howborn/smart-car-freescale/1.3D/整车预览.jpg

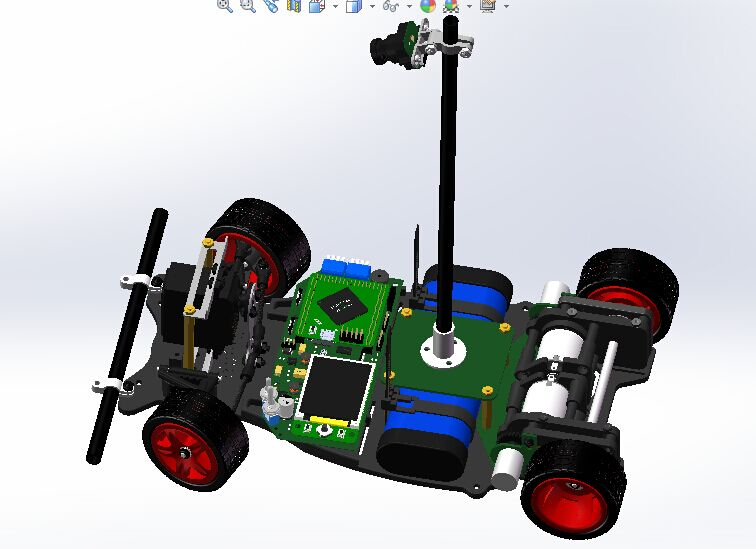
1.3D/整车预览.jpg
