howborn/smart-car-freescale/5.Photos/整车-黑白.jpg

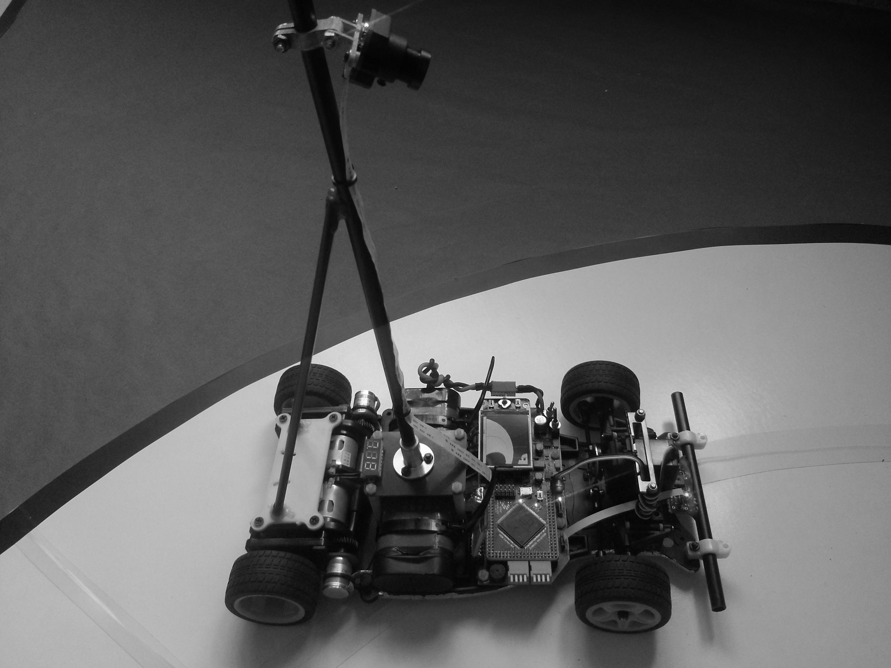
5.Photos/整车-黑白.jpg
