howborn/smart-car-freescale/1.3D/摄像头-三维图/摄像头-1.SLDASM

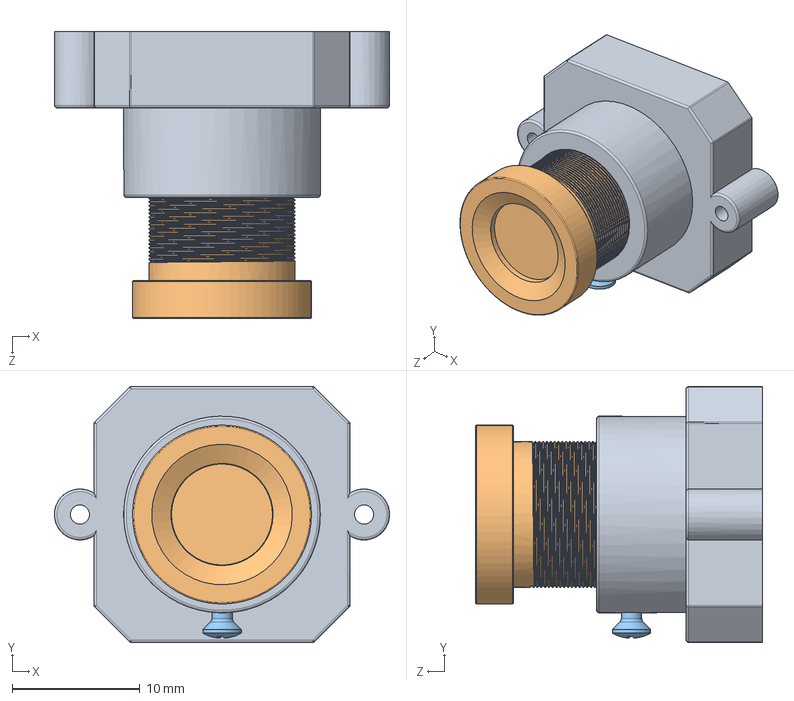
[picture p21: CAD file, 2018-04-18]
1.3D/摄像头-三维图/摄像头-1.SLDASM
26.2 x 20.1 x 22.5 mm
底座
镜头
螺钉
