howborn/smart-car-freescale/1.3D/摄像头-三维图/摄像头.SLDASM

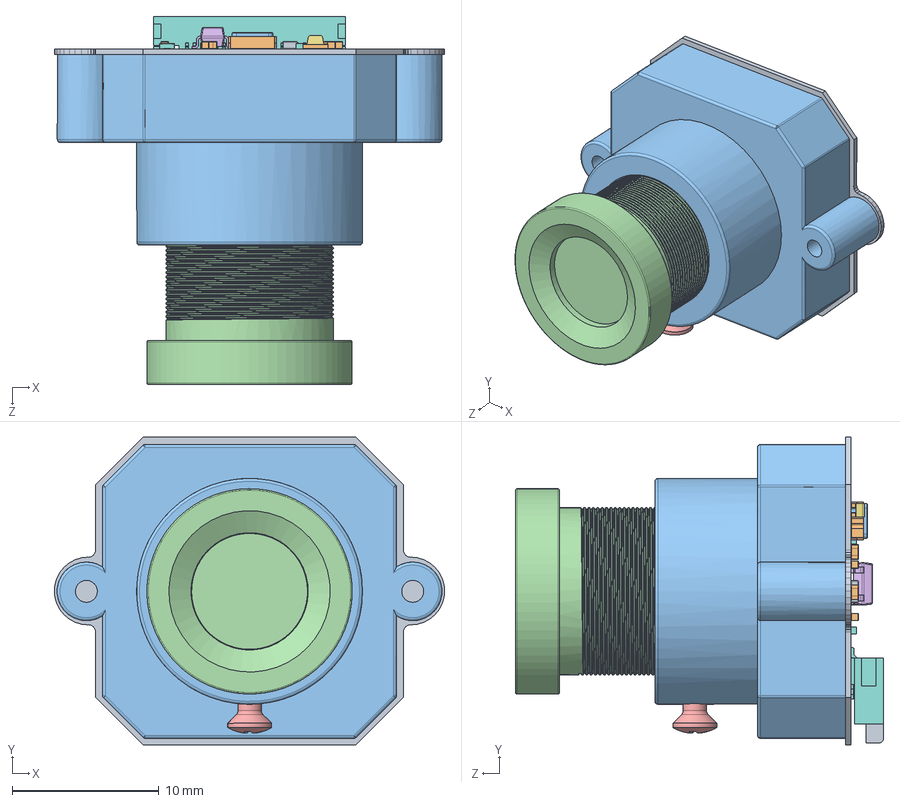
[picture p22: CAD file, 2018-04-18]
1.3D/摄像头-三维图/摄像头.SLDASM
26.6 x 21.0 x 25.1 mm
Board摄像头
User_Library-ASTX-H11_Pad
User_Library-ASTX-H11_Pad001
User_Library-ASTX-H11_Pad002
User_Library-ASTX-H11_ComponentPads
SOT23-5
CLCC-48-11.43x11.43mm
RES-0402 x 4
Chip_Inductor-0402_100505 x 2
User_Library-LTST-C190TBKT_Pad
User_Library-LTST-C190TBKT_Pad005
User_Library-LTST-C190TBKT_Pad001
User_Library-LTST-C190TBKT_Pad004
User_Library-LTST-C190TBKT_Pad003
User_Library-LTST-C190TBKT_Lens
FPC-ZIF-SMD-Horizontal-0.5-18
FPC-ZIF-SMD-Horizontal-0.5-18_2
CAP-0402 x 11
底座
镜头
螺钉
