howborn/smart-car-freescale/1.3D/编码器装配体_右.SLDASM

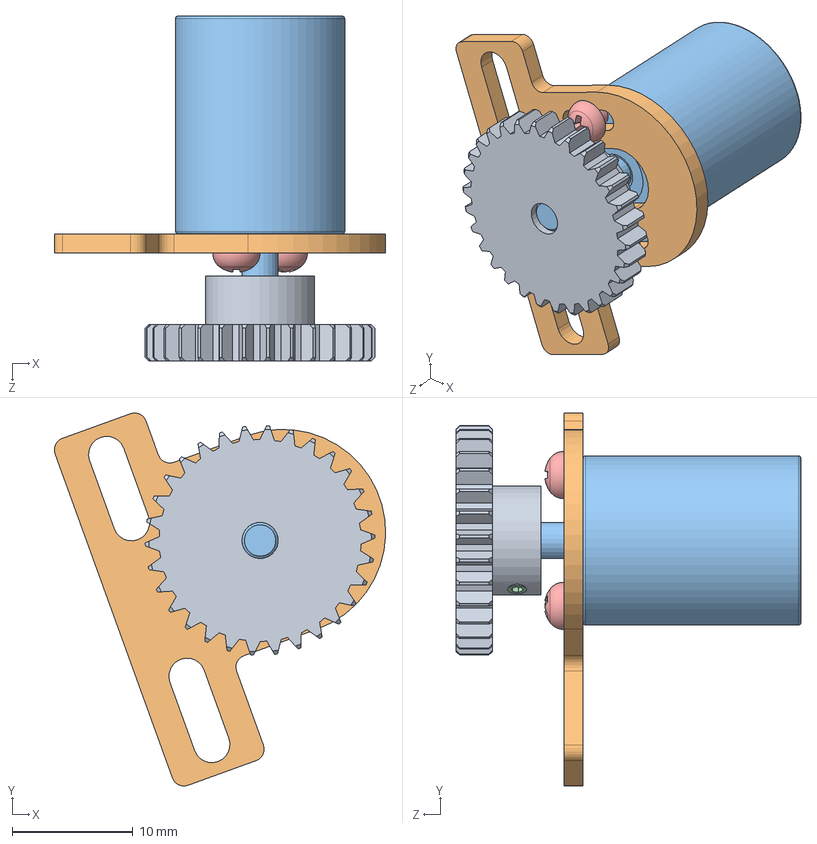
[picture p23: CAD file, 2018-04-18]
1.3D/编码器装配体_右.SLDASM
27.4 x 30.8 x 28.5 mm
编码器齿轮
编码器支架
测速编码器
紧钉螺钉-M2
十字半圆头螺钉-M2 x 2
