howborn/smart-car-freescale/1.3D/主板-三维图/主板_V1.0.SLDASM

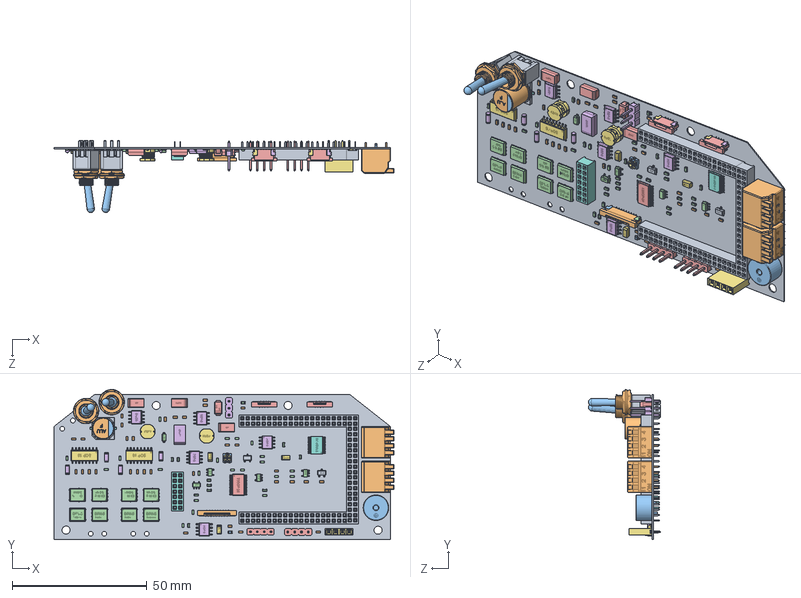
[picture p24: CAD file, 2018-04-18]
1.3D/主板-三维图/主板_V1.0.SLDASM
126.3 x 55.8 x 26.8 mm
Board主板_V1.0
Switch-Piano-DIP-4 x 2
Buzzer_9.5x6
CAP-0603 x 31
CaseC_6032-28 x 3
CaseD_7343-31
CaseA_3216-18 x 3
User_Library-ALU-F_Pins_1
User_Library-ALU-F_Fuss_1
User_Library-ALU-F_K_X_F6rper_1
User_Library-ALU-F_Beschriftung_1
Diode-SOD123
Diode-SMA
Diode-SMD-1206 x 4
Inductor-CD-54 x 2
User_Library-LTST-C190GKT_Pad005
User_Library-LTST-C190GKT_Pad001
User_Library-LTST-C190GKT_Pad004
User_Library-LTST-C190GKT_Pad003
User_Library-LTST-C190GKT_Lens
User_Library-LTST-C190GKT_Pad
User_Library-LTST-C190TBKT_Pad
User_Library-LTST-C190TBKT_Pad005
User_Library-LTST-C190TBKT_Pad001
User_Library-LTST-C190TBKT_Pad004
User_Library-LTST-C190TBKT_Pad003
User_Library-LTST-C190TBKT_Lens
DFN-5-5x6mm x 8
Pin-Header-2.54-Single-4 x 2
Pin-Header-2.54-Single-3
Female-Header-2.54-Single-4
Female-Header-2.00-Double-14
SOT323-3 x 2
RES-0603 x 32
User_Library-PVZ3A_PVZ3A_base_По_умолчанию
User_Library-PVZ3A_Pin1_По_умолчанию
User_Library-PVZ3A_Pin2_По_умолчанию
User_Library-PVZ3A_Pin2_По_умолчанию_2
User_Library-PVZ3A_PVZ3A_res_По_умолчанию
User_Library-PVZ3A_PVZ3A_con_По_умолчанию
SW-SMTS-102-1 x 2
SW-SMTS-102-2 x 2
SW-SMTS-102-3 x 2
SOT23-5 x 4
TSSOP-24
SOP-8 x 5
SOP-16 x 2
TSSOP-20
Female-Header-2.00-Double-40 x 3
ffc_fpc_affc20-18-050-shb-t_01
ffc_fpc_affc20-18-050-shb-t_02
ffc_fpc_affc20-18-050-shb-t_03
ffc_fpc_affc20-08-050-shb-t_01 x 2
ffc_fpc_affc20-08-050-shb-t_02 x 2
ffc_fpc_affc20-08-050-shb-t_03 x 2
