howborn/smart-car-freescale/3.Software/src/control.h

/**
 * --------------Smart_Car工程-----------------
 * @file Control.h
 * @version 0.0
 * @date 2015-2-7
 *
 *
 * 版权所有:  北华航天工学院 第十届飞思卡尔  摄像头2队
 * 硬件平台:  MK60FX512
 * 
 */
#ifndef __CONTROL_H__
#define __CONTROL_H__

void Direction_Control();
void Speed_Control();

#endif
