howborn/smart-car-freescale/3.Software/src/analyze.h

/**
 * --------------Smart_Car工程-----------------
 * @file Analyze.h
 * @version 0.0
 * @date 2015-2-7
 *
 *
 * 版权所有:  北华航天工学院 第十届飞思卡尔  摄像头2队
 * 硬件平台:  MK60FX512
 * 
 */
#ifndef __ANALYZE_H__
#define __ANALYZE_H__

void Find_Line(uint8 image[][H]);
void Get_Center_Line();
void Recognition_Type();

#endif
