howborn/smart-car-freescale/3.Software/src/delay.h

/**
 * --------------Smart_Car工程-----------------
 * @file Delay.h
 * @version 0.0
 * @date 2015-2-7
 *
 *
 * 版权所有:  北华航天工学院 第十届飞思卡尔  摄像头2队
 * 硬件平台:  MK60FX512
 * 
 */
#ifndef __DELAY_H__
#define __DELAY_H__

void Delayms(uint16 ms);
void Delayus(uint16 us);

#endif
