howborn/smart-car-freescale/3.Software/src/k60_card.h

#ifndef __K60_CARD_H__
#define __K60_CARD_H__

/*
 * 系统主频定义(CORE_CLK_MHZ)
 * 可选范围:
 * <MK60F15>
 * PLL_100       //100MHz 
 * PLL_120       //120MHz 是MK60F12的额定最高主频，再往上飞思卡尔可不质保
 * PLL_150       //150MHz 是MK60F15的额定最高主频，再往上飞思卡尔可不质保
 * PLL_180       //180MHz
 * PLL_200       //200MHz 如果超到200，发热很正常，烧了别找我>_>
 */
#if defined(USE_K60F15)
  #define CORE_CLK_MHZ        PLL_180
#endif


/*
 * 总线频率定义(BUS_CLK_MHZ)
 * 可选范围:
 *   不超过系统主频，但建议不超过100，超过100后会出现跑飞、发热现象
 *
*/
#if (defined(USE_K60F15))
  #define BUS_CLK_MHZ         60u
#endif   
/*
 * Flex总线频率定义(FLEXBUS_CLK_MHZ)
 * 可选范围:
 *   不超过50
 *
*/
#define FLEXBUS_CLK_MHZ     50u 
   
/*
 * Flash频率定义(FLASH_CLK_MHZ)
 * 可选范围:
 *   不超过25
 *
*/
#define FLASH_CLK_MHZ       25u    


/* 
 * 选择调试信息输出所有的串口号和波特率
 */
#define TERM_PORT           UART0
#define TERMINAL_BAUD       115200
#define UART_R_PORT         PTB16
#define UART_T_PORT         PTB17

/*
 * 是否启用串口显示调试信息
 * 如果启用，核心板会在运行时通过UART5显示器件相关信息，占用PTE8和PTE9两个端口
 * 1显示  0不显示
 */
#define PRINT_ON_OFF    0

#if (PRINT_ON_OFF == 0)            
  #undef DEBUG_PRINT
#endif
   
/*
 * 是否启用断言函数判断参数合法性
 * 如果启用，会增加部分库函的运行时间来判断参数的合法性
 * 1使用  0不使用
 */
#define ASSERT_ON_OFF   0

#if (ASSERT_ON_OFF == 0)            
  #undef DEBUG_ASSERT
#endif

/*
 * 是否使用uCOS II
 * 1使用  0不使用
 */
#define UCOS_II         0

/*
 * 是否使用FatFs
 * 1使用  0不使用
 */
#define USE_FATFS       1

/*
 * 选择当前USB设备的类型
 * USB_DEVICE_CLASS_CDC
 * USB_DEVICE_CLASS_HID
 */
//#define USB_DEVICE_CLASS USB_DEVICE_CLASS_CDC

/*
 * 定义MCU型号
 */
#if defined(USE_K60F15)
  #define CPU_MK60F15
#else
  #error "未定义CPU类型"
#endif  


#endif /* __K60_CARD_H__ */
