howborn/smart-car-freescale/3.Software/src/gui.h

/**
 * --------------Smart_Car工程-----------------
 * @file Gui.h
 * @version 0.0
 * @date 2015-2-7
 *
 *
 * 版权所有:  北华航天工学院 第十届飞思卡尔  摄像头2队
 * 硬件平台:  MK60FX512
 * 
 */
#ifndef __GUI_H__
#define __GUI_H__

extern int16 Which_Row;
void GUI_Init();
void GUI_Menu(uint8 image[][H]);

#endif
